unloquer/AQA/firmware/src/gps.cpp

#include "app.h"

TinyGPSPlus gpsParser;
SoftwareSerial gpsSerial(13, 7);

void setupGPS() {
  static const int gpsRXPin = 13, gpsTXPin = 7;
  static const uint32_t bauds = 9600;
  gpsSerial.begin(bauds);
}

void readGPS(unsigned long ms) {
  unsigned long start = millis();

  wdt_disable();

  do {
    while(gpsSerial.available()) {
      gpsParser.encode(gpsSerial.read());
    }
  } while (millis() - start < ms);

  wdt_enable(1000);
}

GPSData parseGPSData() {
  GPSData data;

  if (gpsParser.location.isValid()) {
    data.ready = 1;

    data.lat = gpsParser.location.lat();
    data.lng = gpsParser.location.lng();

    DMSG("lat: ");
    DMSG_STR(data.lat);
    DMSG("lng: ");
    DMSG_STR(data.lng);
  } else {
    data.ready = 0;
    DMSG_STR("GPS is not ready!");
    // return data;
  }

  if (gpsParser.date.isValid()) {
    data.date += gpsParser.date.month() + STR_SLASH + gpsParser.date.day() +
      STR_SLASH + gpsParser.date.year();
    DMSG_STR("date: "+data.date);
  }

  if (gpsParser.time.isValid()) {
    String timeStr = "";
    if (gpsParser.time.hour() < 10) timeStr += STR_ZERO;
    timeStr += gpsParser.time.hour();
    timeStr += STR_COLON;

    if (gpsParser.time.minute() < 10) timeStr += STR_ZERO;
    timeStr += gpsParser.time.minute();
    timeStr += STR_COLON;

    if (gpsParser.time.second() < 10) timeStr += STR_ZERO;
    timeStr += gpsParser.time.second();
    timeStr += STR_DOT;

    if (gpsParser.time.centisecond() < 10) timeStr += STR_ZERO;
    timeStr += gpsParser.time.centisecond();

    data.time = timeStr;
    DMSG("time: ");
    DMSG_STR(data.time);
  }

  if(gpsParser.altitude.isValid()) {
    data.altitude = gpsParser.altitude.meters();
    DMSG("altitude: ");
    DMSG_STR(data.altitude);
  }

  if(gpsParser.course.isValid()) {
    data.course = gpsParser.course.deg();
    DMSG("course: ");
    DMSG_STR(data.course);
  }

  if(gpsParser.speed.isValid()) {
    data.speed = gpsParser.speed.kmph();
    DMSG("speed: ");
    DMSG_STR(data.speed);
  }

  return data;
}

GPSData getGPSData() {
  readGPS(800);
  GPSData data = parseGPSData();
  return data;
}
